OnionIoT/Omega2-LTE/Images/O2LTE-face-00.png

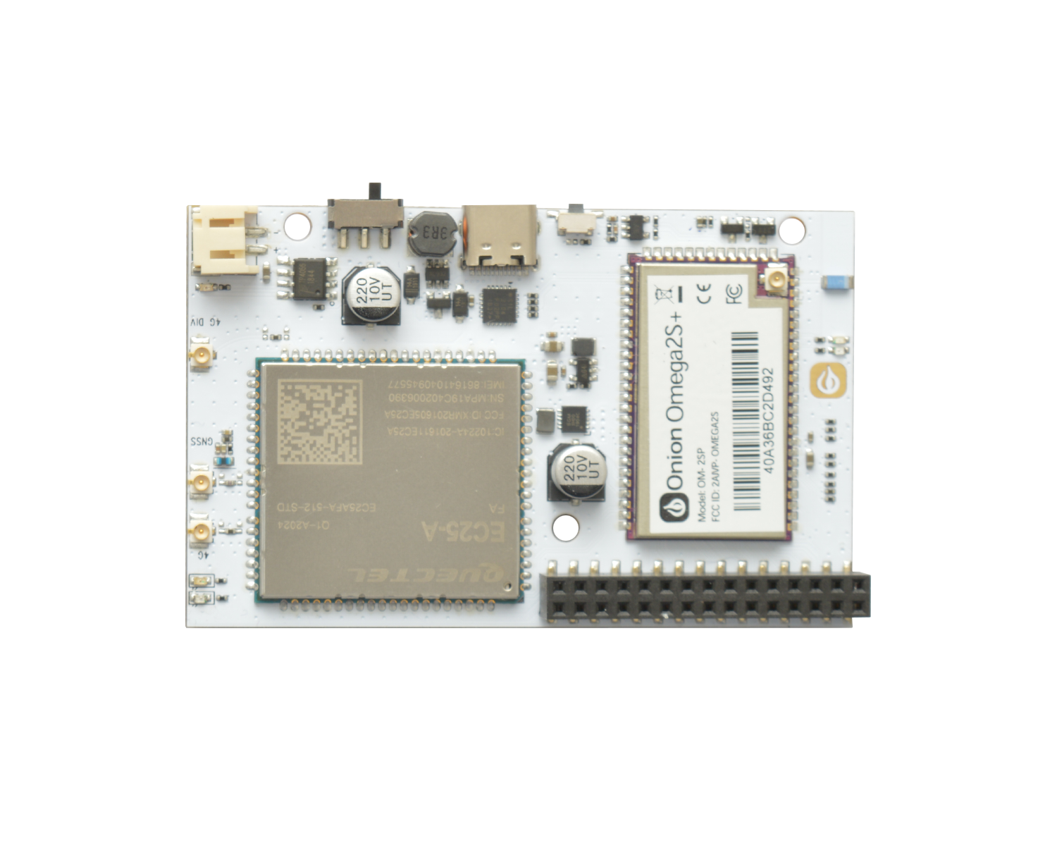
Images/O2LTE-face-00.png
