OnionIoT/Omega2-LTE/Images/O2LTE-sidebyside-01.png

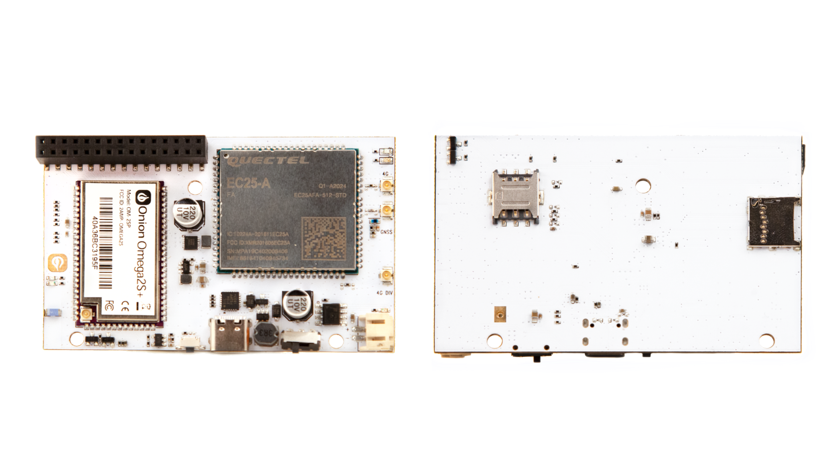
Images/O2LTE-sidebyside-01.png
